bestander/robco-terminal/components/robco_display/menu_state.cpp

#include "menu_state.h"
#include <algorithm>

MenuState::MenuState() {}

void MenuState::start_password_entry(const std::string& prompt) {
    password_entry_mode_ = true;
    password_.clear();
    password_prompt_ = prompt;
}

void MenuState::append_password_char(char c) {
    if (password_entry_mode_)
        password_ += c;
}

void MenuState::remove_password_char() {
    if (password_entry_mode_ && !password_.empty())
        password_.pop_back();
}

bool MenuState::is_password_entry_mode() const {
    return password_entry_mode_;
}

std::string MenuState::get_password() const {
    return password_;
}

void MenuState::end_password_entry() {
    password_entry_mode_ = false;
    password_.clear();
    password_prompt_.clear();
}

std::string MenuState::get_password_prompt() const {
    return password_prompt_;
}

void MenuState::set_boot_messages(const std::vector<std::string>& messages) {
    boot_messages_ = messages;
}

void MenuState::set_menu(const std::vector<MenuEntry>& menu) {
    menu_ = menu;
}

void MenuState::on_key_press(uint8_t keycode) {
    auto is_navigable_type = [](MenuEntry::Type type) {
        return type == MenuEntry::Type::ACTION || type == MenuEntry::Type::SUBMENU;
    };
    auto set_first_navigable = [&](const std::vector<MenuEntry>* menu) {
        for (size_t i = 0; i < menu->size(); ++i) {
            if (is_navigable_type((*menu)[i].type)) {
                selected_index_ = i;
                return;
            }
        }
        selected_index_ = -11;
    };
    if (!boot_complete_) {
        boot_complete_ = true;
        set_first_navigable(&menu_);
        return;
    }
    std::vector<MenuEntry>* current_menu = &menu_;
    for (size_t i = 0; i < menu_stack_.size(); ++i) {
        int idx = menu_stack_[i];
        if (idx >= 0 && idx < current_menu->size()) {
            current_menu = &(*current_menu)[idx].subitems;
        }
    }
    int menu_size = current_menu->size();
    if (menu_size == 0) return;
    auto is_navigable = [&](int idx) {
        return is_navigable_type((*current_menu)[idx].type);
    };
    if (keycode == 0x52) { // Up
        int next = selected_index_;
        do {
            next = (next - 1 + menu_size) % menu_size;
        } while (!is_navigable(next) && next != selected_index_);
        if (is_navigable(next)) selected_index_ = next;
    } else if (keycode == 0x51) { // Down
        int next = selected_index_;
        do {
            next = (next + 1) % menu_size;
        } while (!is_navigable(next) && next != selected_index_);
        if (is_navigable(next)) selected_index_ = next;
    } else if (keycode == 0x28) { // Enter
        if ((*current_menu)[selected_index_].type == MenuEntry::Type::SUBMENU) {
            menu_stack_.push_back(selected_index_);
            set_first_navigable(&(*current_menu)[selected_index_].subitems);
        }
    } else if (keycode == 0x29) { // Escape
        if (!menu_stack_.empty()) {
            selected_index_ = menu_stack_.back();
            menu_stack_.pop_back();
        }
    }
}

const std::vector<std::string>& MenuState::get_boot_messages() const {
    return boot_messages_;
}

bool MenuState::is_boot_complete() const {
    return boot_complete_;
}

const MenuEntry* MenuState::get_current_menu() const {
    if (menu_stack_.empty()) return nullptr;
    return &menu_[menu_stack_.back()];
}

int MenuState::get_selected_index() const {
    return selected_index_;
}

void MenuState::set_header(const std::vector<std::string>& header) {
    header_lines_ = header;
}

std::string MenuState::get_display_text() const {
    if (!boot_complete_) {
        std::string text;
        for (const auto& line : boot_messages_) text += line + "\n";
        return text;
    }
    std::string header_text;
    for (const auto& header : header_lines_) {
        header_text += header + "\n";
    }
    if (password_entry_mode_) {
        std::string masked(password_.size(), '*');
        return header_text + password_prompt_ + "\n" + masked;
    }
    const std::vector<MenuEntry>* current_menu = &menu_;
    for (size_t i = 0; i < menu_stack_.size(); ++i) {
        int idx = menu_stack_[i];
        if (idx >= 0 && idx < current_menu->size()) {
            current_menu = &(*current_menu)[idx].subitems;
        }
    }
    std::string text = "";
    for (size_t i = 0; i < current_menu->size(); ++i) {
        std::string line = (i == selected_index_ ? "> " : "  ") + (*current_menu)[i].title;
        if ((*current_menu)[i].type == MenuEntry::Type::STATUS && !(*current_menu)[i].status_value.empty()) {
            line += ": " + (*current_menu)[i].status_value;
        }
        text += line + "\n";
    }
    return header_text + text;
}

void MenuState::add_log(const std::string& entry) {
    logs_.push_back(entry);
}

void MenuState::remove_log(int index) {
    if (index >= 0 && index < logs_.size()) logs_.erase(logs_.begin() + index);
}

const std::vector<std::string>& MenuState::get_logs() const {
    return logs_;
}

void MenuState::set_status(const std::string& value) {
    status_value_ = value;
}

std::string MenuState::get_status() const {
    return status_value_;
}
