bestander/robco-terminal/components/robco_display/menu_state.h

#pragma once
#include <string>
#include <vector>
#include <cstdint>


struct MenuEntry {
    std::string title;
    enum class Type { STATIC, SUBMENU, ACTION, STATUS, LOGS } type;
    std::vector<MenuEntry> subitems;
    std::vector<std::string> logs;
    std::string status_value;
};


class MenuState {
public:
    MenuState();
    // Password entry mode
    void start_password_entry(const std::string& prompt);
    void append_password_char(char c);
    void remove_password_char();
    bool is_password_entry_mode() const;
    std::string get_password() const;
    void end_password_entry();
    std::string get_password_prompt() const;
    void set_header(const std::vector<std::string>& header);
    void set_boot_messages(const std::vector<std::string>& messages);
    void set_menu(const std::vector<MenuEntry>& menu);
    void on_key_press(uint8_t keycode);
    const std::vector<std::string>& get_boot_messages() const;
    bool is_boot_complete() const;
    const MenuEntry* get_current_menu() const;
    int get_selected_index() const;
    std::string get_display_text() const;
    void add_log(const std::string& entry);
    void remove_log(int index);
    const std::vector<std::string>& get_logs() const;
    void set_status(const std::string& value);
    std::string get_status() const;
    std::vector<MenuEntry>& get_menu();
    const std::vector<int>& get_menu_stack() const { return menu_stack_; }
private:
    std::vector<std::string> header_lines_;
    std::vector<std::string> boot_messages_;
    bool boot_complete_ = false;
    std::vector<MenuEntry> menu_;
    int selected_index_ = 0;
    int current_menu_level_ = 0;
    std::vector<int> menu_stack_;
    std::vector<std::string> logs_;
    std::string status_value_;
    // Password entry state
    bool password_entry_mode_ = false;
    std::string password_;
    std::string password_prompt_;
};
