bestander/robco-terminal/components/robco_display/FSEX302.c

/*******************************************************************************
 * Size: 24 px
 * Bpp: 1
 * Opts: --bpp 1 --size 24 --no-compress --stride 1 --align 1 --font FSEX302.ttf --range 32-126 --format lvgl -o fixedsys.c
 ******************************************************************************/

#ifdef __has_include
    #if __has_include("lvgl.h")
        #ifndef LV_LVGL_H_INCLUDE_SIMPLE
            #define LV_LVGL_H_INCLUDE_SIMPLE
        #endif
    #endif
#endif

#ifdef LV_LVGL_H_INCLUDE_SIMPLE
    #include "lvgl.h"
#else
    #include "lvgl/lvgl.h"
#endif



#ifndef FIXEDSYS
#define FIXEDSYS 1
#endif

#if FIXEDSYS

/*-----------------
 *    BITMAPS
 *----------------*/

/*Store the image of the glyphs*/
static LV_ATTRIBUTE_LARGE_CONST const uint8_t glyph_bitmap[] = {
    /* U+0020 " " */
    0x0,

    /* U+0021 "!" */
    0x38, 0xef, 0xff, 0xff, 0xf3, 0x8e, 0x38, 0x0,
    0xe, 0x38, 0xe0,

    /* U+0022 "\"" */
    0xe3, 0xf1, 0xf8, 0xfc, 0x70,

    /* U+0023 "#" */
    0x39, 0xc7, 0x38, 0xe7, 0x7f, 0xf3, 0x9c, 0x73,
    0x8e, 0x71, 0xce, 0x39, 0xc7, 0x3b, 0xff, 0x9c,
    0xe3, 0x9c, 0x73, 0x80,

    /* U+0024 "$" */
    0x1c, 0xe, 0x7, 0x7, 0xee, 0x3f, 0x3, 0x80,
    0x40, 0x38, 0xe, 0x7, 0x0, 0xe0, 0x38, 0x1f,
    0x8e, 0x46, 0x3f, 0xe, 0x7, 0x3, 0x80,

    /* U+0025 "%" */
    0x7c, 0xe, 0x70, 0xe7, 0x6e, 0x76, 0x7c, 0xe0,
    0x48, 0x3, 0x80, 0x70, 0x1c, 0x1, 0xc0, 0x7b,
    0xe6, 0xb6, 0x67, 0x70, 0x77, 0x7, 0x70, 0x3e,

    /* U+0026 "&" */
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

    /* U+007D "}" */
    0xe0, 0x38, 0x38, 0x38, 0x38, 0x38, 0x1c, 0x4,
    0x7, 0x1c, 0x38, 0x38, 0x38, 0x38, 0x38, 0xe0,

    /* U+007E "~" */
    0x3c, 0x6, 0x87, 0xdd, 0xe3, 0xac, 0x7c
};


/*---------------------
 *  GLYPH DESCRIPTION
 *--------------------*/

static const lv_font_fmt_txt_glyph_dsc_t glyph_dsc[] = {
    {.bitmap_index = 0, .adv_w = 0, .box_w = 0, .box_h = 0, .ofs_x = 0, .ofs_y = 0} /* id = 0 reserved */,
    {.bitmap_index = 0, .adv_w = 192, .box_w = 1, .box_h = 1, .ofs_x = 0, .ofs_y = 0},
    {.bitmap_index = 1, .adv_w = 192, .box_w = 6, .box_h = 14, .ofs_x = 3, .ofs_y = 0},
    {.bitmap_index = 12, .adv_w = 192, .box_w = 9, .box_h = 4, .ofs_x = 1, .ofs_y = 10},
    {.bitmap_index = 17, .adv_w = 192, .box_w = 11, .box_h = 14, .ofs_x = 1, .ofs_y = 0},
    {.bitmap_index = 37, .adv_w = 192, .box_w = 9, .box_h = 20, .ofs_x = 1, .ofs_y = -3},
    {.bitmap_index = 60, .adv_w = 192, .box_w = 12, .box_h = 16, .ofs_x = 0, .ofs_y = -1},
    {.bitmap_index = 84, .adv_w = 192, .box_w = 11, .box_h = 14, .ofs_x = 1, .ofs_y = 0},
    {.bitmap_index = 104, .adv_w = 192, .box_w = 3, .box_h = 4, .ofs_x = 4, .ofs_y = 10},
    {.bitmap_index = 106, .adv_w = 192, .box_w = 6, .box_h = 16, .ofs_x = 3, .ofs_y = -2},
    {.bitmap_index = 118, .adv_w = 192, .box_w = 6, .box_h = 16, .ofs_x = 3, .ofs_y = -2},
    {.bitmap_index = 130, .adv_w = 192, .box_w = 11, .box_h = 7, .ofs_x = 1, .ofs_y = 4},
    {.bitmap_index = 140, .adv_w = 192, .box_w = 9, .box_h = 8, .ofs_x = 1, .ofs_y = 3},
    {.bitmap_index = 149, .adv_w = 192, .box_w = 5, .box_h = 6, .ofs_x = 4, .ofs_y = -3},
    {.bitmap_index = 153, .adv_w = 192, .box_w = 9, .box_h = 1, .ofs_x = 1, .ofs_y = 7},
    {.bitmap_index = 155, .adv_w = 192, .box_w = 5, .box_h = 3, .ofs_x = 4, .ofs_y = 0},
    {.bitmap_index = 157, .adv_w = 192, .box_w = 9, .box_h = 15, .ofs_x = 1, .ofs_y = -1},
    {.bitmap_index = 174, .adv_w = 192, .box_w = 9, .box_h = 14, .ofs_x = 1, .ofs_y = 0},
    {.bitmap_index = 190, .adv_w = 192, .box_w = 8, .box_h = 14, .ofs_x = 1, .ofs_y = 0},
    {.bitmap_index = 204, .adv_w = 192, .box_w = 9, .box_h = 14, .ofs_x = 1, .ofs_y = 0},
    {.bitmap_index = 220, .adv_w = 192, .box_w = 9, .box_h = 14, .ofs_x = 1, .ofs_y = 0},
    {.bitmap_index = 236, .adv_w = 192, .box_w = 11, .box_h = 14, .ofs_x = 1, .ofs_y = 0},
    {.bitmap_index = 256, .adv_w = 192, .box_w = 9, .box_h = 14, .ofs_x = 1, .ofs_y = 0},
    {.bitmap_index = 272, .adv_w = 192, .box_w = 9, .box_h = 14, .ofs_x = 1, .ofs_y = 0},
    {.bitmap_index = 288, .adv_w = 192, .box_w = 10, .box_h = 14, .ofs_x = 1, .ofs_y = 0},
    {.bitmap_index = 306, .adv_w = 192, .box_w = 9, .box_h = 14, .ofs_x = 1, .ofs_y = 0},
    {.bitmap_index = 322, .adv_w = 192, .box_w = 9, .box_h = 14, .ofs_x = 1, .ofs_y = 0},
    {.bitmap_index = 338, .adv_w = 192, .box_w = 5, .box_h = 11, .ofs_x = 4, .ofs_y = 0},
    {.bitmap_index = 345, .adv_w = 192, .box_w = 5, .box_h = 14, .ofs_x = 4, .ofs_y = -3},
    {.bitmap_index = 354, .adv_w = 192, .box_w = 9, .box_h = 14, .ofs_x = 1, .ofs_y = 0},
    {.bitmap_index = 370, .adv_w = 192, .box_w = 9, .box_h = 4, .ofs_x = 1, .ofs_y = 5},
    {.bitmap_index = 375, .adv_w = 192, .box_w = 9, .box_h = 14, .ofs_x = 1, .ofs_y = 0},
    {.bitmap_index = 391, .adv_w = 192, .box_w = 9, .box_h = 14, .ofs_x = 1, .ofs_y = 0},
    {.bitmap_index = 407, .adv_w = 192, .box_w = 12, .box_h = 14, .ofs_x = 0, .ofs_y = 0},
    {.bitmap_index = 428, .adv_w = 192, .box_w = 9, .box_h = 14, .ofs_x = 1, .ofs_y = 0},
    {.bitmap_index = 444, .adv_w = 192, .box_w = 9, .box_h = 14, .ofs_x = 1, .ofs_y = 0},
    {.bitmap_index = 460, .adv_w = 192, .box_w = 9, .box_h = 14, .ofs_x = 1, .ofs_y = 0},
    {.bitmap_index = 476, .adv_w = 192, .box_w = 9, .box_h = 14, .ofs_x = 1, .ofs_y = 0},
    {.bitmap_index = 492, .adv_w = 192, .box_w = 9, .box_h = 14, .ofs_x = 1, .ofs_y = 0},
    {.bitmap_index = 508, .adv_w = 192, .box_w = 9, .box_h = 14, .ofs_x = 1, .ofs_y = 0},
    {.bitmap_index = 524, .adv_w = 192, .box_w = 9, .box_h = 14, .ofs_x = 1, .ofs_y = 0},
    {.bitmap_index = 540, .adv_w = 192, .box_w = 9, .box_h = 14, .ofs_x = 1, .ofs_y = 0},
    {.bitmap_index = 556, .adv_w = 192, .box_w = 6, .box_h = 14, .ofs_x = 3, .ofs_y = 0},
    {.bitmap_index = 567, .adv_w = 192, .box_w = 9, .box_h = 14, .ofs_x = 1, .ofs_y = 0},
    {.bitmap_index = 583, .adv_w = 192, .box_w = 9, .box_h = 14, .ofs_x = 1, .ofs_y = 0},
    {.bitmap_index = 599, .adv_w = 192, .box_w = 9, .box_h = 14, .ofs_x = 1, .ofs_y = 0},
    {.bitmap_index = 615, .adv_w = 192, .box_w = 11, .box_h = 14, .ofs_x = 1, .ofs_y = 0},
    {.bitmap_index = 635, .adv_w = 192, .box_w = 11, .box_h = 14, .ofs_x = 1, .ofs_y = 0},
    {.bitmap_index = 655, .adv_w = 192, .box_w = 9, .box_h = 14, .ofs_x = 1, .ofs_y = 0},
    {.bitmap_index = 671, .adv_w = 192, .box_w = 9, .box_h = 14, .ofs_x = 1, .ofs_y = 0},
    {.bitmap_index = 687, .adv_w = 192, .box_w = 9, .box_h = 17, .ofs_x = 1, .ofs_y = -3},
    {.bitmap_index = 707, .adv_w = 192, .box_w = 9, .box_h = 14, .ofs_x = 1, .ofs_y = 0},
    {.bitmap_index = 723, .adv_w = 192, .box_w = 9, .box_h = 14, .ofs_x = 1, .ofs_y = 0},
    {.bitmap_index = 739, .adv_w = 192, .box_w = 9, .box_h = 14, .ofs_x = 1, .ofs_y = 0},
    {.bitmap_index = 755, .adv_w = 192, .box_w = 9, .box_h = 14, .ofs_x = 1, .ofs_y = 0},
    {.bitmap_index = 771, .adv_w = 192, .box_w = 9, .box_h = 14, .ofs_x = 1, .ofs_y = 0},
    {.bitmap_index = 787, .adv_w = 192, .box_w = 11, .box_h = 14, .ofs_x = 1, .ofs_y = 0},
    {.bitmap_index = 807, .adv_w = 192, .box_w = 9, .box_h = 14, .ofs_x = 1, .ofs_y = 0},
    {.bitmap_index = 823, .adv_w = 192, .box_w = 9, .box_h = 14, .ofs_x = 1, .ofs_y = 0},
    {.bitmap_index = 839, .adv_w = 192, .box_w = 9, .box_h = 14, .ofs_x = 1, .ofs_y = 0},
    {.bitmap_index = 855, .adv_w = 192, .box_w = 6, .box_h = 19, .ofs_x = 3, .ofs_y = -5},
    {.bitmap_index = 870, .adv_w = 192, .box_w = 9, .box_h = 15, .ofs_x = 1, .ofs_y = -1},
    {.bitmap_index = 887, .adv_w = 192, .box_w = 6, .box_h = 19, .ofs_x = 3, .ofs_y = -5},
    {.bitmap_index = 902, .adv_w = 192, .box_w = 9, .box_h = 5, .ofs_x = 1, .ofs_y = 13},
    {.bitmap_index = 908, .adv_w = 192, .box_w = 12, .box_h = 1, .ofs_x = 0, .ofs_y = -4},
    {.bitmap_index = 910, .adv_w = 192, .box_w = 7, .box_h = 4, .ofs_x = 2, .ofs_y = 13},
    {.bitmap_index = 914, .adv_w = 192, .box_w = 9, .box_h = 11, .ofs_x = 1, .ofs_y = 0},
    {.bitmap_index = 927, .adv_w = 192, .box_w = 9, .box_h = 14, .ofs_x = 1, .ofs_y = 0},
    {.bitmap_index = 943, .adv_w = 192, .box_w = 9, .box_h = 11, .ofs_x = 1, .ofs_y = 0},
    {.bitmap_index = 956, .adv_w = 192, .box_w = 9, .box_h = 14, .ofs_x = 1, .ofs_y = 0},
    {.bitmap_index = 972, .adv_w = 192, .box_w = 9, .box_h = 11, .ofs_x = 1, .ofs_y = 0},
    {.bitmap_index = 985, .adv_w = 192, .box_w = 9, .box_h = 14, .ofs_x = 1, .ofs_y = 0},
    {.bitmap_index = 1001, .adv_w = 192, .box_w = 9, .box_h = 16, .ofs_x = 1, .ofs_y = -5},
    {.bitmap_index = 1019, .adv_w = 192, .box_w = 9, .box_h = 14, .ofs_x = 1, .ofs_y = 0},
    {.bitmap_index = 1035, .adv_w = 192, .box_w = 9, .box_h = 16, .ofs_x = 1, .ofs_y = 0},
    {.bitmap_index = 1053, .adv_w = 192, .box_w = 8, .box_h = 20, .ofs_x = 1, .ofs_y = -5},
    {.bitmap_index = 1073, .adv_w = 192, .box_w = 9, .box_h = 14, .ofs_x = 1, .ofs_y = 0},
    {.bitmap_index = 1089, .adv_w = 192, .box_w = 9, .box_h = 14, .ofs_x = 1, .ofs_y = 0},
    {.bitmap_index = 1105, .adv_w = 192, .box_w = 11, .box_h = 11, .ofs_x = 1, .ofs_y = 0},
    {.bitmap_index = 1121, .adv_w = 192, .box_w = 9, .box_h = 11, .ofs_x = 1, .ofs_y = 0},
    {.bitmap_index = 1134, .adv_w = 192, .box_w = 9, .box_h = 11, .ofs_x = 1, .ofs_y = 0},
    {.bitmap_index = 1147, .adv_w = 192, .box_w = 9, .box_h = 16, .ofs_x = 1, .ofs_y = -5},
    {.bitmap_index = 1165, .adv_w = 192, .box_w = 9, .box_h = 16, .ofs_x = 1, .ofs_y = -5},
    {.bitmap_index = 1183, .adv_w = 192, .box_w = 9, .box_h = 11, .ofs_x = 1, .ofs_y = 0},
    {.bitmap_index = 1196, .adv_w = 192, .box_w = 9, .box_h = 11, .ofs_x = 1, .ofs_y = 0},
    {.bitmap_index = 1209, .adv_w = 192, .box_w = 9, .box_h = 14, .ofs_x = 1, .ofs_y = 0},
    {.bitmap_index = 1225, .adv_w = 192, .box_w = 9, .box_h = 11, .ofs_x = 1, .ofs_y = 0},
    {.bitmap_index = 1238, .adv_w = 192, .box_w = 9, .box_h = 11, .ofs_x = 1, .ofs_y = 0},
    {.bitmap_index = 1251, .adv_w = 192, .box_w = 11, .box_h = 11, .ofs_x = 1, .ofs_y = 0},
    {.bitmap_index = 1267, .adv_w = 192, .box_w = 9, .box_h = 11, .ofs_x = 1, .ofs_y = 0},
    {.bitmap_index = 1280, .adv_w = 192, .box_w = 11, .box_h = 16, .ofs_x = 0, .ofs_y = -5},
    {.bitmap_index = 1302, .adv_w = 192, .box_w = 9, .box_h = 11, .ofs_x = 1, .ofs_y = 0},
    {.bitmap_index = 1315, .adv_w = 192, .box_w = 8, .box_h = 16, .ofs_x = 1, .ofs_y = -2},
    {.bitmap_index = 1331, .adv_w = 192, .box_w = 3, .box_h = 19, .ofs_x = 4, .ofs_y = -5},
    {.bitmap_index = 1339, .adv_w = 192, .box_w = 8, .box_h = 16, .ofs_x = 3, .ofs_y = -2},
    {.bitmap_index = 1355, .adv_w = 192, .box_w = 11, .box_h = 5, .ofs_x = 0, .ofs_y = 10}
};

/*---------------------
 *  CHARACTER MAPPING
 *--------------------*/



/*Collect the unicode lists and glyph_id offsets*/
static const lv_font_fmt_txt_cmap_t cmaps[] =
{
    {
        .range_start = 32, .range_length = 95, .glyph_id_start = 1,
        .unicode_list = NULL, .glyph_id_ofs_list = NULL, .list_length = 0, .type = LV_FONT_FMT_TXT_CMAP_FORMAT0_TINY
    }
};



/*--------------------
 *  ALL CUSTOM DATA
 *--------------------*/

#if LVGL_VERSION_MAJOR == 8
/*Store all the custom data of the font*/
static  lv_font_fmt_txt_glyph_cache_t cache;
#endif

#if LVGL_VERSION_MAJOR >= 8
static const lv_font_fmt_txt_dsc_t font_dsc = {
#else
static lv_font_fmt_txt_dsc_t font_dsc = {
#endif
    .glyph_bitmap = glyph_bitmap,
    .glyph_dsc = glyph_dsc,
    .cmaps = cmaps,
    .kern_dsc = NULL,
    .kern_scale = 0,
    .cmap_num = 1,
    .bpp = 1,
    .kern_classes = 0,
    .bitmap_format = 0,
#if LVGL_VERSION_MAJOR == 8
    .cache = &cache
#endif

};



/*-----------------
 *  PUBLIC FONT
 *----------------*/

/*Initialize a public general font descriptor*/
#if LVGL_VERSION_MAJOR >= 8
const lv_font_t fixedsys = {
#else
lv_font_t fixedsys = {
#endif
    .get_glyph_dsc = lv_font_get_glyph_dsc_fmt_txt,    /*Function pointer to get glyph's data*/
    .get_glyph_bitmap = lv_font_get_bitmap_fmt_txt,    /*Function pointer to get glyph's bitmap*/
    .line_height = 23,          /*The maximum line height required by the font*/
    .base_line = 5,             /*Baseline measured from the bottom of the line*/
#if !(LVGL_VERSION_MAJOR == 6 && LVGL_VERSION_MINOR == 0)
    .subpx = LV_FONT_SUBPX_NONE,
#endif
#if LV_VERSION_CHECK(7, 4, 0) || LVGL_VERSION_MAJOR >= 8
    .underline_position = -2,
    .underline_thickness = 2,
#endif
    .dsc = &font_dsc,          /*The custom font data. Will be accessed by `get_glyph_bitmap/dsc` */
#if LV_VERSION_CHECK(8, 2, 0) || LVGL_VERSION_MAJOR >= 9
    .fallback = NULL,
#endif
    .user_data = NULL,
};



#endif /*#if FIXEDSYS*/
