bestander/robco-terminal/components/robco_display/bsp.h

#ifndef BSP_H
#define BSP_H

#include "driver/gpio.h"
#include "esp_lcd_panel_rgb.h"
#include "esp_lcd_touch_gt911.h"

#define BSP_LCD_BK_LIGHT_ON_LEVEL 1
#define BSP_LCD_BK_LIGHT_OFF_LEVEL (!BSP_LCD_BK_LIGHT_ON_LEVEL)
#define BSP_LCD_GPIO_BK_LIGHT GPIO_NUM_2
#define BSP_LCD_GPIO_HSYNC GPIO_NUM_39
#define BSP_LCD_GPIO_VSYNC GPIO_NUM_40
#define BSP_LCD_GPIO_DE GPIO_NUM_41
#define BSP_LCD_GPIO_PCLK GPIO_NUM_42
#define BSP_LCD_GPIO_DATA() { \
    GPIO_NUM_15,                 \
    GPIO_NUM_7,                  \
    GPIO_NUM_6,                  \
    GPIO_NUM_5,                  \
    GPIO_NUM_4,                  \
    GPIO_NUM_9,                  \
    GPIO_NUM_46,                 \
    GPIO_NUM_3,                  \
    GPIO_NUM_8,                  \
    GPIO_NUM_16,                 \
    GPIO_NUM_1,                  \
    GPIO_NUM_14,                 \
    GPIO_NUM_21,                 \
    GPIO_NUM_47,                 \
    GPIO_NUM_48,                 \
    GPIO_NUM_45,                 \
}
#define BSP_LCD_GPIO_DISP GPIO_NUM_NC

// The pixel number in horizontal and vertical
#define BSP_LCD_H_RES 800
#define BSP_LCD_V_RES 480

#define BSP_LCD_PANEL_TIMING()         \
    (esp_lcd_rgb_timing_t)             \
    {                                  \
        .pclk_hz = 12000000,           \
        .h_res = BSP_LCD_H_RES,        \
        .v_res = BSP_LCD_V_RES,        \
        .hsync_pulse_width = 30,       \
        .hsync_back_porch = 16,        \
        .hsync_front_porch = 20,       \
        .vsync_pulse_width = 20,       \
        .vsync_back_porch = 20,        \
        .vsync_front_porch = 30,       \
        .flags = { .pclk_active_neg = true } \
    }

#define BSP_TOUCH_GPIO_SCL GPIO_NUM_20
#define BSP_TOUCH_GPIO_SDA GPIO_NUM_19
#define BSP_TOUCH_GPIO_INT GPIO_NUM_NC
#define BSP_TOUCH_GPIO_RST GPIO_NUM_38

#endif
